jimahlstrom/HL2IOBoard/zl2te_arduino/fcode2bcode.ino

// This is firmware for the Hermes Lite 2 IO board designed by Jim Ahlstrom, N2ADR. It is
//   Copyright (c) 2022-2023 James C. Ahlstrom <jahlstr@gmail.com>.
//   It is licensed under the MIT license. See MIT.txt.

// Return the band code given the frequency code.
// The band code is a frequency code close to the center of the band.

//#include "hl2ioboard.h"

uint8_t fcode2band(uint8_t fcode)
{
	uint8_t Fcode2Band[256] = {0,
	31, 31, 31, 31, 31, 31, 31, 31, 31, 31, 31, 31, 31, 31, 31, 31, 31, 31, 31, 31, 
	31, 31, 31, 31, 31, 31, 31, 31, 31, 31, 31, 31, 31, 31, 31, 31, 31, 31, 31, 31, 
	31, 31, 31, 50, 50, 50, 50, 50, 50, 50, 50, 50, 50, 50, 50, 50, 50, 50, 50, 50, 
	50, 50, 50, 71, 71, 71, 71, 71, 71, 71, 71, 71, 71, 71, 71, 71, 71, 82, 82, 82, 
	82, 82, 82, 82, 82, 88, 88, 88, 88, 88, 92, 92, 92, 92, 97, 97, 97, 97, 97, 97, 
	103, 103, 103, 103, 106, 106, 106, 109, 109, 109, 111, 111, 114, 114, 114, 114, 114, 114, 114, 123, 
	123, 123, 123, 123, 123, 127, 127, 127, 127, 127, 127, 127, 127, 127, 139, 139, 139, 139, 139, 139, 
	139, 139, 145, 145, 145, 145, 145, 145, 145, 145, 155, 155, 155, 155, 155, 155, 155, 155, 155, 155, 
	155, 155, 167, 167, 167, 167, 167, 167, 167, 172, 172, 172, 172, 172, 172, 172, 172, 182, 182, 182, 
	182, 182, 182, 182, 187, 187, 187, 187, 187, 187, 187, 187, 196, 196, 196, 196, 196, 196, 196, 196, 
	204, 204, 204, 204, 204, 204, 204, 204, 204, 204, 204, 204, 204, 204, 204, 204, 204, 204, 204, 204, 
	204, 204, 204, 204, 204, 204, 204, 204, 204, 204, 204, 204, 204, 204, 204, 204, 204, 204, 204, 204, 
	204, 204, 204, 204, 204, 204, 204, 204, 204, 204, 204, 204, 204, 204, 204 };

	return Fcode2Band[fcode];
}
